costarc/CoCo_FPGA_Hat/Reference Designs/Multi_Cartridge/Tools/Downland.vhdl

library IEEE;
use IEEE.std_logic_1164.all;
use ieee.numeric_std.all;

entity rom is
	port(
		cs		: in std_logic;
		A		: in std_logic_vector(15 downto 0);
		D		: out std_logic_vector(7 downto 0)
	);
end rom;

architecture rtl of rom is
type MEMORY is array ( 0 to 8191 ) of std_logic_vector(7 downto 0);
constant rom : MEMORY := (
    x"12",
    x"1a",
    x"50",
    x"10",
    x"ce",
    x"01",
    x"9f",
    x"8e",
    x"00",
    x"00",
    x"6f",
    x"80",
    x"8c",
    x"40",
    x"00",
    x"26",
    x"f9",
    x"86",
    x"7e",
    x"b7",
    x"01",
    x"0c",
    x"8e",
    x"dc",
    x"4d",
    x"bf",
    x"01",
    x"0d",
    x"86",
    x"35",
    x"b7",
    x"ff",
    x"03",
    x"86",
    x"20",
    x"b7",
    x"ff",
    x"98",
    x"86",
    x"fe",
    x"b7",
    x"ff",
    x"02",
    x"b6",
    x"ff",
    x"00",
    x"84",
    x"10",
    x"26",
    x"0f",
    x"cc",
    x"00",
    x"09",
    x"fd",
    x"ff",
    x"b4",
    x"cc",
    x"24",
    x"3f",
    x"fd",
    x"ff",
    x"b6",
    x"86",
    x"e8",
    x"8c",
    x"86",
    x"f8",
    x"97",
    x"6a",
    x"bd",
    x"c2",
    x"01",
    x"cc",
    x"1c",
    x"00",
    x"bd",
    x"cd",
    x"f7",
    x"bd",
    x"cd",
    x"e3",
    x"4f",
    x"bd",
    x"c1",
    x"f6",
    x"bd",
    x"c2",
    x"17",
    x"b7",
    x"ff",
    x"de",
    x"8e",
    x"c0",
    x"00",
    x"9f",
    x"61",
    x"9f",
    x"72",
    x"86",
    x"55",
    x"97",
    x"71",
    x"bd",
    x"db",
    x"ad",
    x"0c",
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
    x"ff",
    x"00",
    x"fe",
    x"00",
    x"fe",
    x"01",
    x"ff",
    x"01",
    x"ff",
    x"00",
    x"fe",
    x"00",
    x"fe",
    x"01",
    x"ff",
    x"01",
    x"ff",
    x"00",
    x"fe",
    x"00",
    x"fe",
    x"01",
    x"ff",
    x"01",
    x"ff",
    x"00",
    x"fe",
    x"00",
    x"fe",
    x"01",
    x"ff",
    x"01",
    x"ff",
    x"00",
    x"fe",
    x"00",
    x"fe",
    x"01",
    x"ff",
    x"01",
    x"ff",
    x"00",
    x"fe",
    x"00",
    x"fe",
    x"01",
    x"ff",
    x"01",
    x"ff",
    x"00",
    x"fe",
    x"00",
    x"fe",
    x"01",
    x"ff",
    x"01",
    x"ff",
    x"00",
    x"fe",
    x"00",
    x"fe",
    x"01",
    x"ff",
    x"01",
    x"ff",
    x"00",
    x"fe",
    x"00",
    x"fe",
    x"01",
    x"ff",
    x"01",
    x"ff",
    x"00",
    x"fe",
    x"00",
    x"fe",
    x"01",
    x"ff",
    x"f7",
    x"ff"
);
begin

process (cs)
begin
if rising_edge(cs) then
    D <= rom(to_integer(unsigned(A)));
end if;
end process;
end;
